Borsh8m3/Intelligent_Cam_System/code/Video detection/Machine/malgorzata_boratynska.jpg

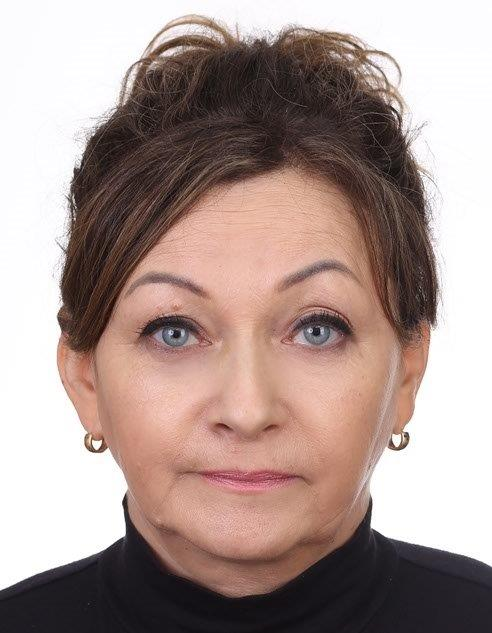
code/Video detection/Machine/malgorzata_boratynska.jpg
