Borsh8m3/Intelligent_Cam_System/code/Video detection/Machine/radzia_suchowiecka.jpg

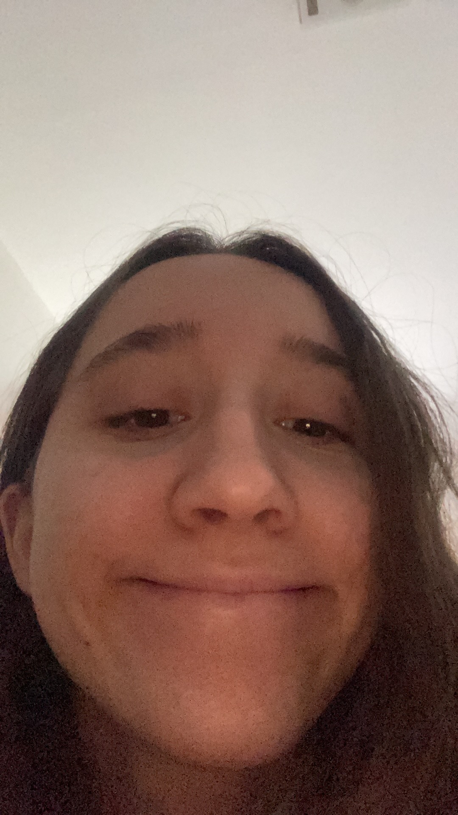
code/Video detection/Machine/radzia_suchowiecka.jpg
