Borsh8m3/Intelligent_Cam_System/documents/DHT11.png

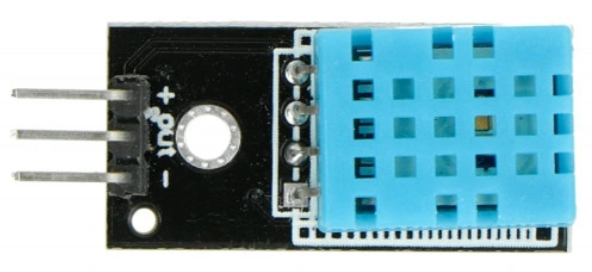
documents/DHT11.png
