Borsh8m3/Intelligent_Cam_System/documents/RSB PICO.png

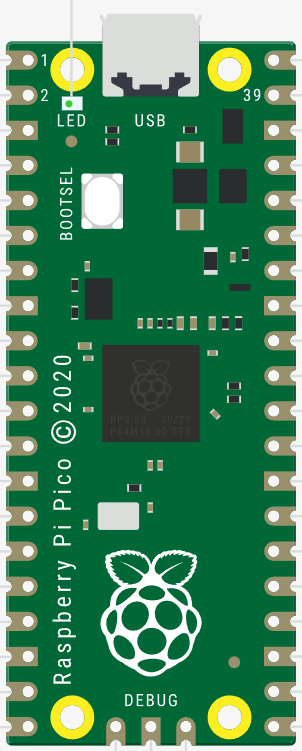
documents/RSB PICO.png
