Borsh8m3/Intelligent_Cam_System/Photographic documentation/Bramka_transzystorowa.png

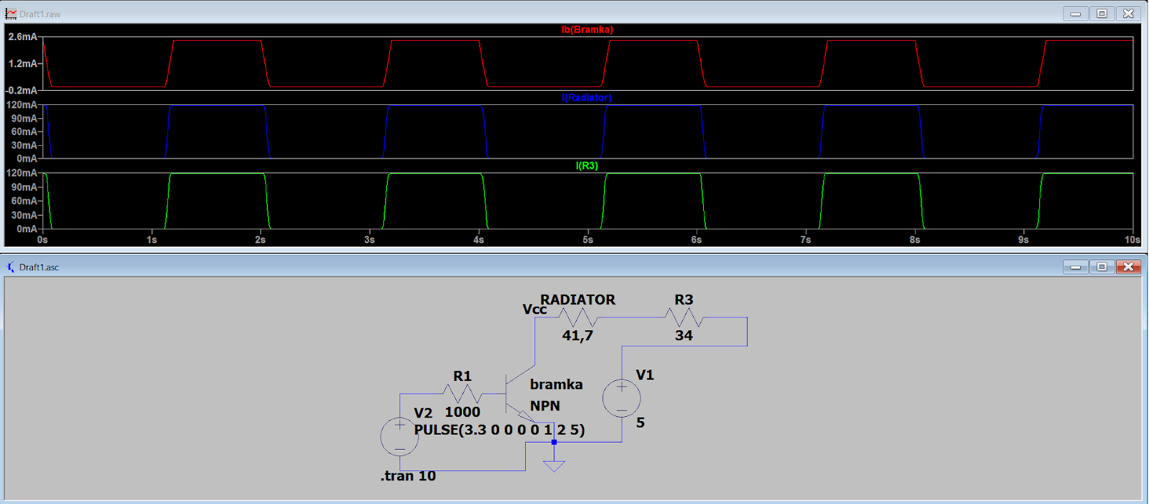
Photographic documentation/Bramka_transzystorowa.png
