Borsh8m3/Intelligent_Cam_System/Photographic documentation/case_inside.png

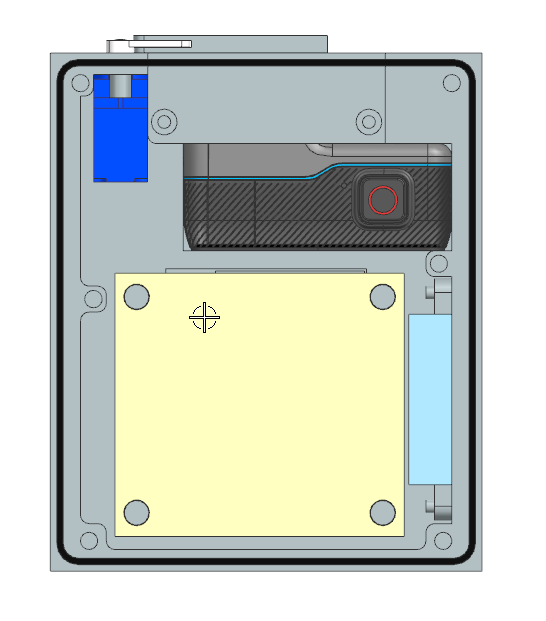
Photographic documentation/case_inside.png
