Borsh8m3/Intelligent_Cam_System/Draft1.asc

bramka: npn; BC547B
R1: res; 1000
R3: res; 34
RADIATOR: res; 41,7
V1: voltage; 5
V2: voltage; PULSE(3.3 0 0 0 0 1 2 5)
Named nets: 0, Vcc
.tran 10
